Khajan352/Offline-Flyback-Charger-30w/simulation/flyback-30w.asc

C1: cap; 2.2n; V=450
C2: cap; 470µ; V=25 Rser=0.04
C3: cap; 470µ; V=400 Rser=0.03
C4: cap; 200µ; V=25 Rser=0.05
C5: cap; 10n
C6: cap; 470µ; V=25 Rser=0.04
C7: cap; 470p
C8: cap; 0.1n
C9: cap; 22µ; V=25
C10: cap; 0.1µ
C11: cap; 1.8n
C12: cap; 100µ; V=400
D1: diode; RFNL5BGE6S
D2: diode; MBR20100CT
D3: diode; RFNL5BGE6S
D4: diode; RFNL5BGE6S
D5: diode; RFNL5BGE6S
D6: diode; VS-E5PH3006
D7: diode; BZX84B22VLY
D8: diode; BZX84B20VLY
D9: diode; BAT54
L1: ind; 300µ; Rser=1m
L2: ind; 12µ; Rser=1m
L3: ind; 2.2µ; Ipk=3 Rser=1m
L4: ind; 10µ; Rser=1m
M1: nmos; STW11NM80
Q1: pnp; 2N2907
Q2: pnp; 2N2907
R2: res; 13.33
R3: res; 47K
R4: res; 75K
R5: res; 10.135K
R6: res; 1K
R7: res; 10R
R8: res; 1K
R9: res; 1K
R10: res; 4.7K
R11: res; 139R
R12: res; 1K
R13: res; 150K
R14: res; 0.5R
R15: res; 39
R16: res; 10K
U1: 
U2: PC817A
U3: LT1242
V1: voltage; SINE(0 220 50)
Named nets: 0
.tran 2
K L1 L2 L4 0.999
.include tl431.lib
