Khajan352/Offline-Flyback-Charger-30w/simulation/ovp.asc

D1: diode; BZX84C22VLY
Q1: pnp; 2N2907
Q2: pnp; 2N2907
R1: res; 4.7K
R2: res; 1K
R3: res; 2.7K
V1: voltage; PWL(0 0 50m 30 100m 0)
Named nets: 0, Out
.tran 100m
