Khajan352/Offline-Flyback-Charger-30w/simulation/window-voltage-protection.asc

R1: res; 32K
R2: res; 100
R3: res; 96K
R4: res; 1K
R5: res; 1K
U1: TLV431
U2: TLV431
V1: voltage; 5V
V2: voltage; PWL(0 0 100m 450)
Named nets: 0, Out
.tran 100m
.include tl431.lib
